pabloestrado/CH32Meteostation/src/funconfig.h

#ifndef _FUNCONFIG_H
#define _FUNCONFIG_H

#define CH32V003           1
//#define FUNCONF_USE_UARTPRINTF 1
//#define FUNCONF_UART_PRINTF_BAUD 9600
#define FUNCONF_USE_DEBUGRINTF 0

#define SYSTICK_USE_HCLK 1
#define FUNCONF_SYSTEM_CORE_CLOCK 24000000 / 4
#define FUNCONF_USE_PLL 0

#endif
